avoccado/avoccado-pcb-avr/avoccado-alpha-1/20140912-A1-gerber-files/rendered/ScreenShot_1.png

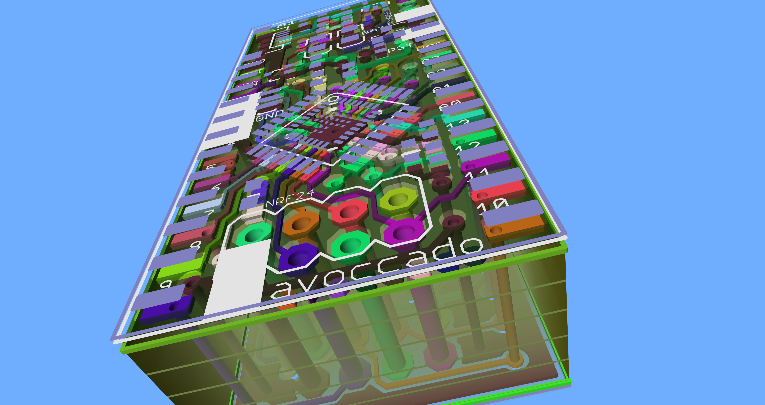
avoccado-alpha-1/20140912-A1-gerber-files/rendered/ScreenShot_1.png
