avoccado/avoccado-pcb-avr/avoccado-faye/avoccado-faye.png

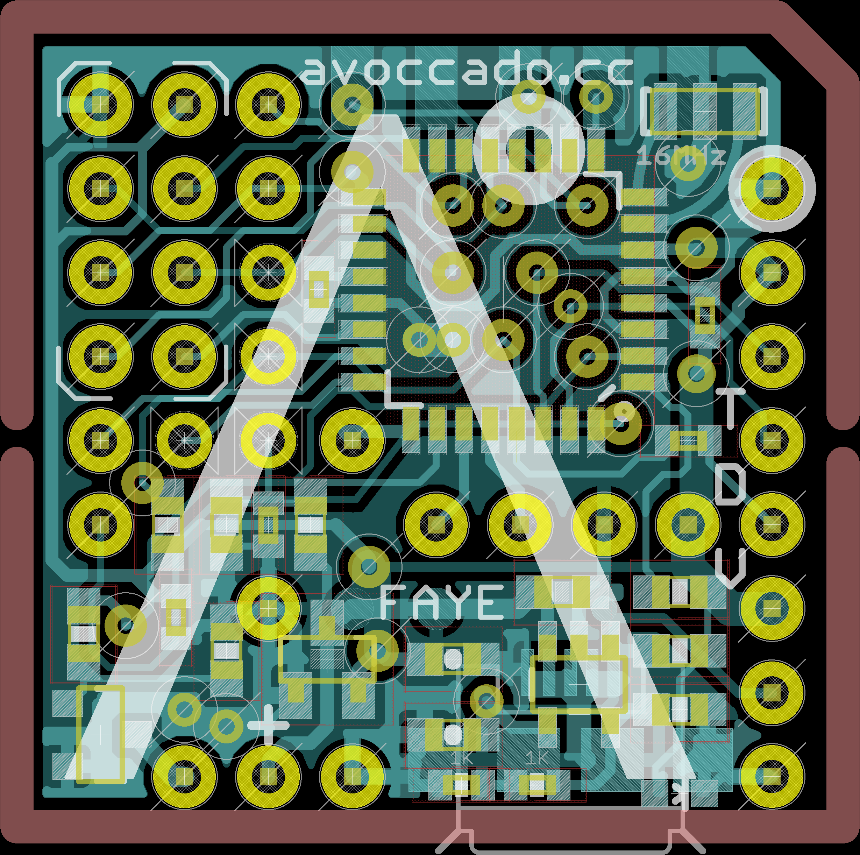
avoccado-faye/avoccado-faye.png
