avoccado/avoccado-pcb-avr/avoccado-felina/avoccado-avr-pcb-felina-all.png

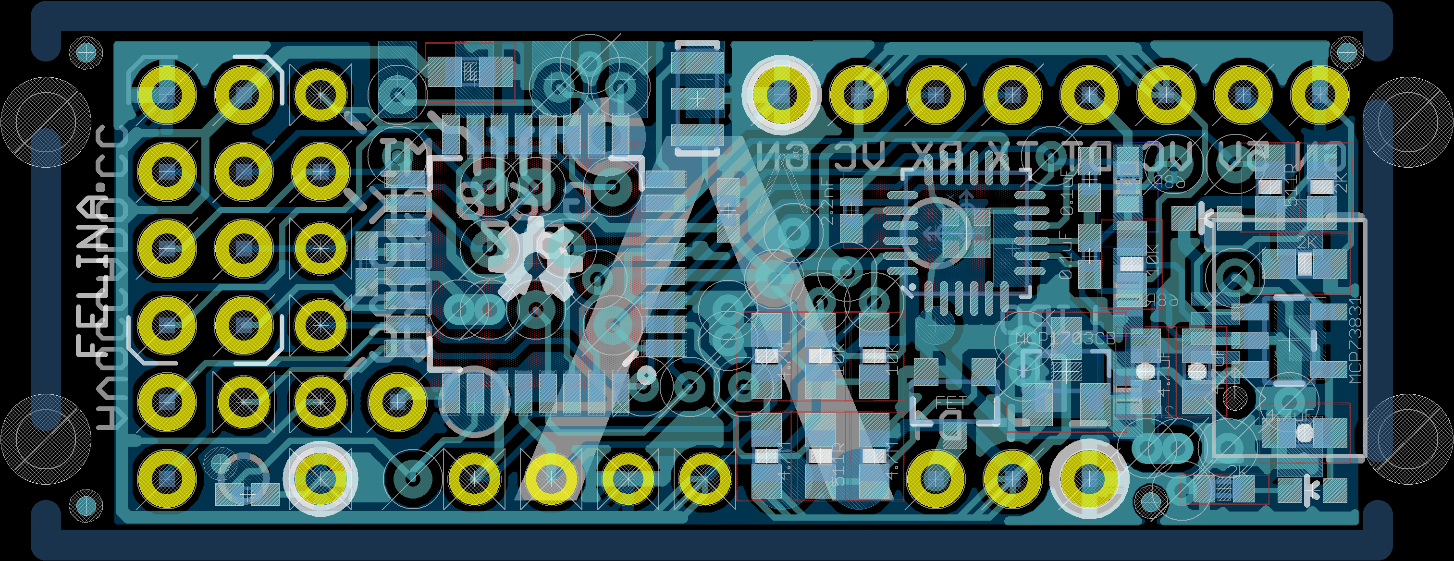
avoccado-felina/avoccado-avr-pcb-felina-all.png
