avoccado/avoccado-pcb-avr/avoccado-felina/avoccado-avr-pcb-felina-bottom.png

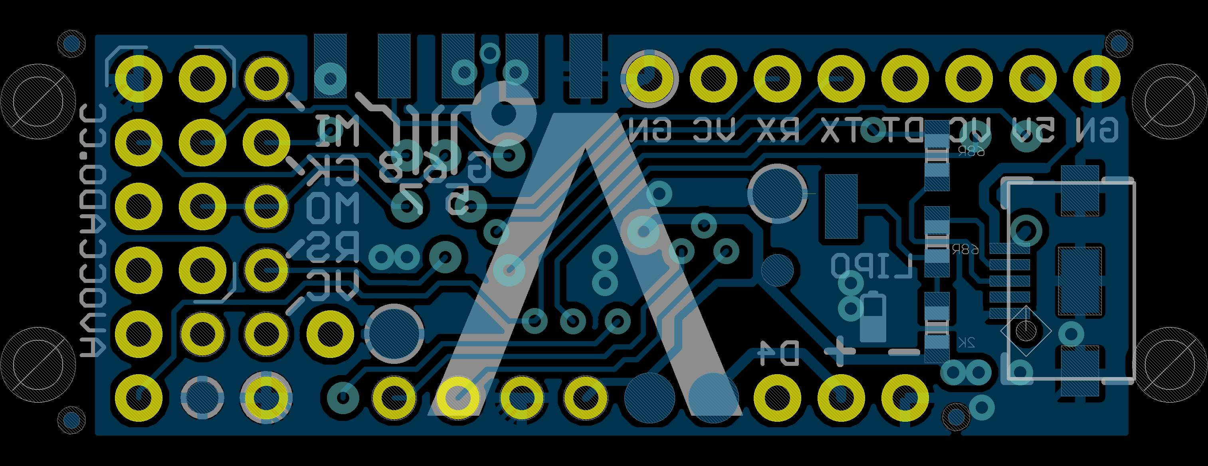
avoccado-felina/avoccado-avr-pcb-felina-bottom.png
