avoccado/avoccado-pcb-avr/avoccado-felina/avoccado-avr-pcb-felina-top.png

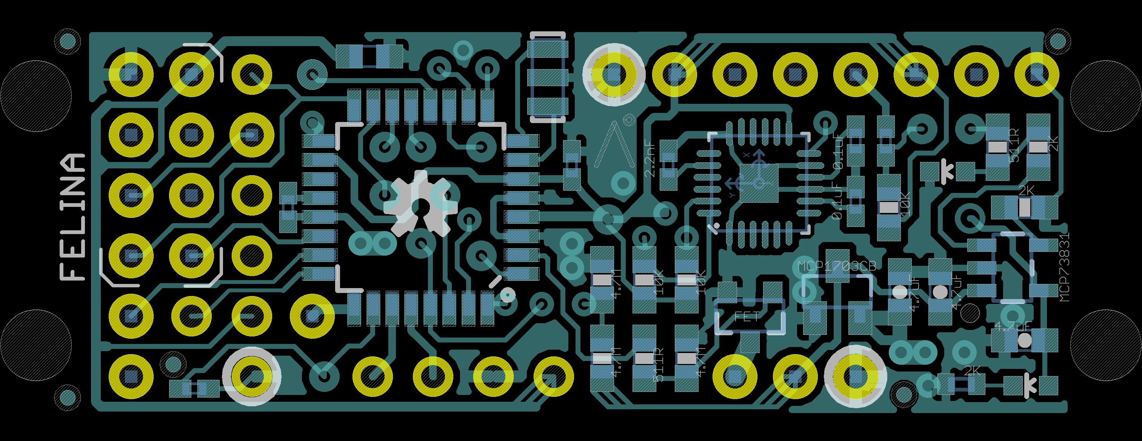
avoccado-felina/avoccado-avr-pcb-felina-top.png
