avoccado/avoccado-pcb-avr/avoccado-gin/avoccado-avr-gin-bot.png

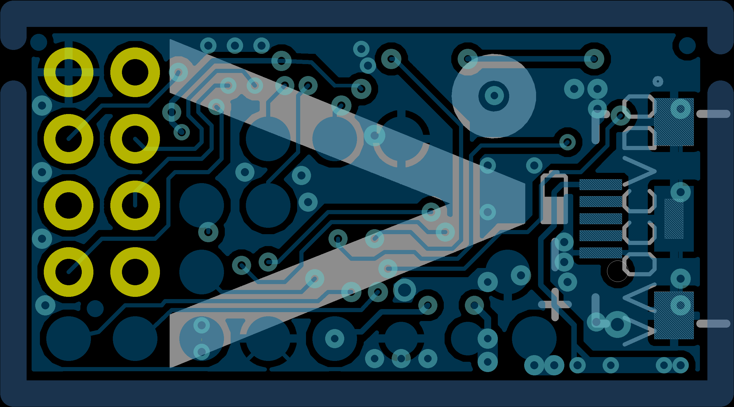
avoccado-gin/avoccado-avr-gin-bot.png
