avoccado/avoccado-pcb-avr/avoccado-nora/nora1-panel/nora1-panel-solder-paste-stencil.png

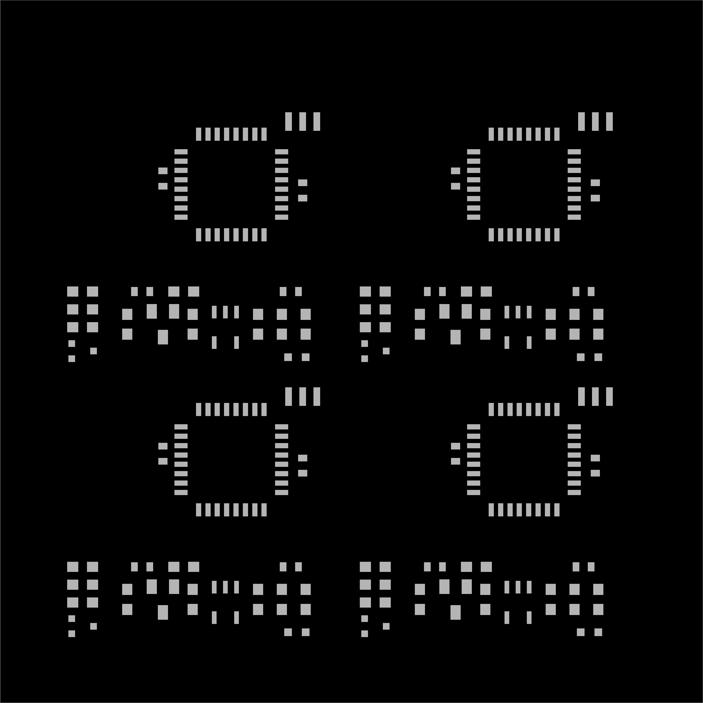
avoccado-nora/nora1-panel/nora1-panel-solder-paste-stencil.png
