avoccado/avoccado-pcb-avr/avoccado-alpha-1/avoccado-avr-pcb.brd

## EAGLE design avoccado-alpha-1/avoccado-avr-pcb.brd (2014-12-11)

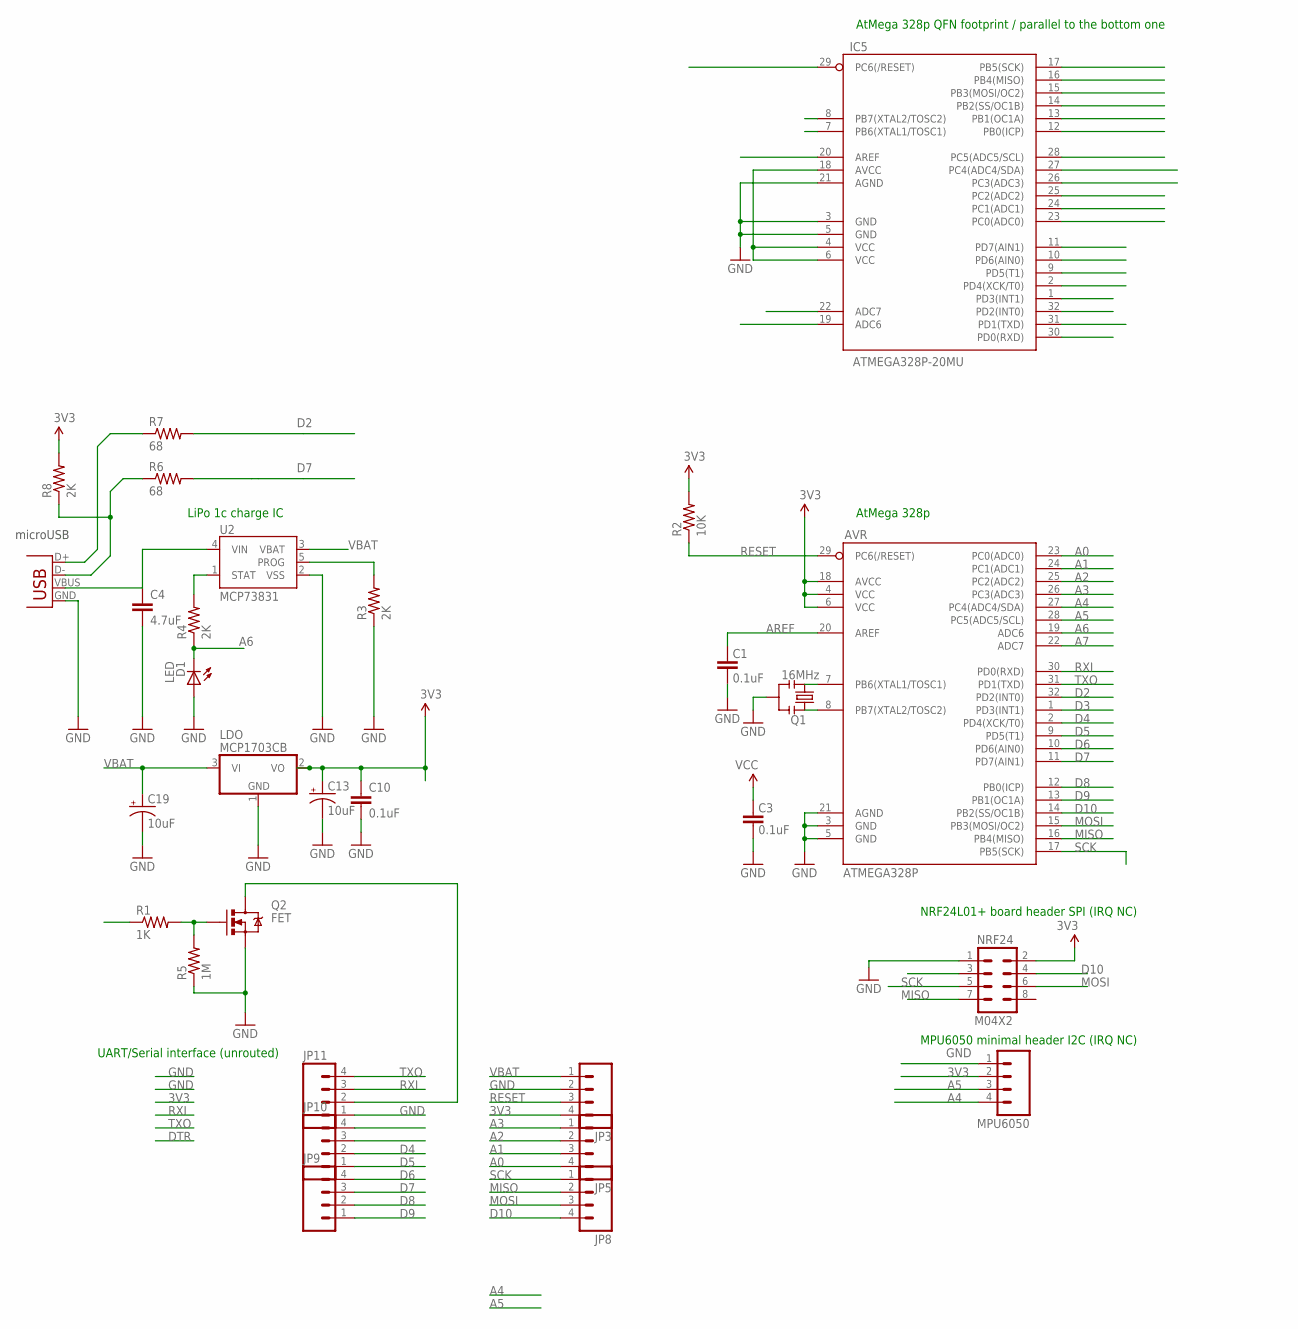
[picture p42: schematic avoccado-avr-pcb.sch]

Parts:
AVR: ATMEGA328P; TQFP32-08
C1, C3, C10: 0.1uF; C0402
C4: 4.7uF; 0603-CAP
C13, C19: 10uF; EIA3216
D1: LED; LED-0603
IC5: ATMEGA328P-20MU; MLF32
JP3, JP5, JP8, JP9, JP10, JP11: M04SMD1X4; 1X04-SMD
LDO: MCP1703CB; SOT23
MPU6050: M041X04_NO_SILK; 1X04_NO_SILK
NRF24: M04X2; 2X4
Q1: 16MHz; RESONATOR-SMD
Q2: FET; SOT323
R1: 1K; 0603-RES
R2: 10K; 0603-RES
R3, R4, R8: 2K; 0603-RES
R5: 1M; 0603-RES
R6, R7: 68; 0603-RES
U2: MCP73831; SOT23-5
X1: Micro USB; USB-MICROB

Connections:
3V3: AVR.4 (VCC), AVR.6 (VCC), AVR.18 (AVCC), C3.2, C10.1, C13.A (+), IC5.4 (VCC), IC5.6 (VCC), IC5.18 (AVCC), JP3.4, LDO.2 (VO), MPU6050.2, NRF24.2, R2.2, R8.2
A0: AVR.23 (PC0(ADC0)), IC5.23 (PC0(ADC0)), JP5.4
A1: AVR.24 (PC1(ADC1)), IC5.24 (PC1(ADC1)), JP5.3
A2: AVR.25 (PC2(ADC2)), IC5.25 (PC2(ADC2)), JP5.2
A3: AVR.26 (PC3(ADC3)), IC5.26 (PC3(ADC3)), JP5.1
A4: AVR.27 (PC4(ADC4/SDA)), IC5.27 (PC4(ADC4/SDA)), MPU6050.4
A5: AVR.28 (PC5(ADC5/SCL)), IC5.28 (PC5(ADC5/SCL)), MPU6050.3
A6: AVR.19 (ADC6), D1.C, IC5.19 (ADC6), R4.1
A7: AVR.22 (ADC7), IC5.22 (ADC7)
AREF: AVR.20 (AREF), C1.2, IC5.20 (AREF)
BUS: C4.1, U2.4 (VIN), X1.VBUS
D2: AVR.32 (PD2(INT0)), IC5.32 (PD2(INT0)), R7.2
D3: AVR.1 (PD3(INT1)), IC5.1 (PD3(INT1)), R1.1
D4: AVR.2 (PD4(XCK/T0)), IC5.2 (PD4(XCK/T0)), JP10.2
D5: AVR.9 (PD5(T1)), IC5.9 (PD5(T1)), JP10.1
D6: AVR.10 (PD6(AIN0)), IC5.10 (PD6(AIN0)), JP9.4
D7: AVR.11 (PD7(AIN1)), IC5.11 (PD7(AIN1)), JP9.3, R6.2
D8: AVR.12 (PB0(ICP)), IC5.12 (PB0(ICP)), JP9.2
D9: AVR.13 (PB1(OC1A)), IC5.13 (PB1(OC1A)), JP9.1, NRF24.3
D10: AVR.14 (PB2(SS/OC1B)), IC5.14 (PB2(SS/OC1B)), JP8.4, NRF24.4
GND: AVR.3 (GND), AVR.5 (GND), AVR.21 (AGND), C1.1, C3.1, C4.2, C10.2, C13.C (-), C19.C (-), D1.A, IC5.3 (GND), IC5.5 (GND), IC5.21 (AGND), JP3.2, JP10.3, JP10.4, JP11.1, LDO.1 (GND), MPU6050.1, NRF24.1, Q1.2, Q2.2 (S), R3.1, R5.1, U2.2 (VSS), X1.GND
MISO: AVR.16 (PB4(MISO)), IC5.16 (PB4(MISO)), JP8.2, NRF24.7
MOSI: AVR.15 (PB3(MOSI/OC2)), IC5.15 (PB3(MOSI/OC2)), JP8.3, NRF24.6
unnamed: AVR.8 (PB7(XTAL2/TOSC2)), IC5.8 (PB7(XTAL2/TOSC2)), Q1.1
unnamed: AVR.7 (PB6(XTAL1/TOSC1)), IC5.7 (PB6(XTAL1/TOSC1)), Q1.3
unnamed: R3.2, U2.5 (PROG)
unnamed: R4.2, U2.1 (STAT)
unnamed: Q2.1 (G), R1.2, R5.2
RESET: AVR.29 (PC6(/RESET)), IC5.29 (PC6(/RESET)), JP3.3, R2.1
RXI: AVR.30 (PD0(RXD)), IC5.30 (PD0(RXD)), JP11.3
SCK: AVR.17 (PB5(SCK)), IC5.17 (PB5(SCK)), JP8.1, NRF24.5
TXO: AVR.31 (PD1(TXD)), IC5.31 (PD1(TXD)), JP11.4
USB-D+: R7.1, X1.D+
USB-D-: R6.1, R8.1, X1.D-
VBAT: C19.A (+), JP3.1, LDO.3 (VI), U2.3 (VBAT)
VIBR: JP11.2, Q2.3 (D)

Notes on the sheet:
microUSB
NRF24L01+ board header SPI (IRQ NC)
MPU6050 minimal header I2C (IRQ NC)
AtMega 328p
AtMega 328p QFN footprint / parallel to the bottom one
LiPo 1c charge IC
UART/Serial interface (unrouted)

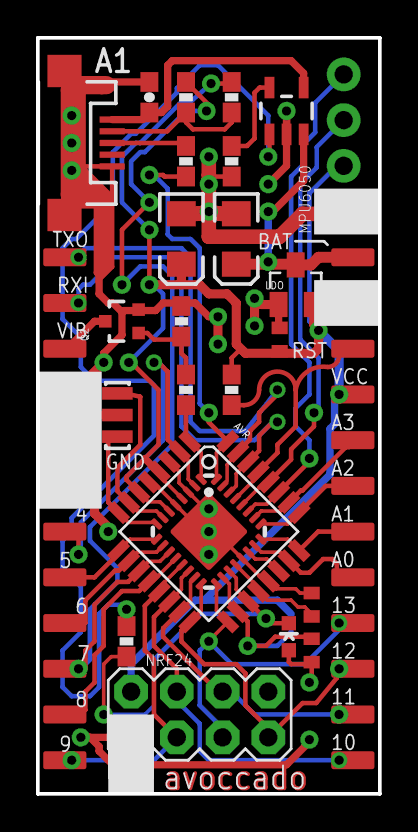
[picture p43: board avoccado-avr-pcb.brd from above]

Board: 2 copper layers, 19.0 x 42.0 mm, 30 parts (0 on the bottom side), 36 nets.
