avoccado/avoccado-pcb-avr/avoccado-yolandi/panel/avoccado-avr-pcb-yolandi-panel.brd

## EAGLE design avoccado-yolandi/panel/avoccado-avr-pcb-yolandi-panel.brd (2015-01-10)

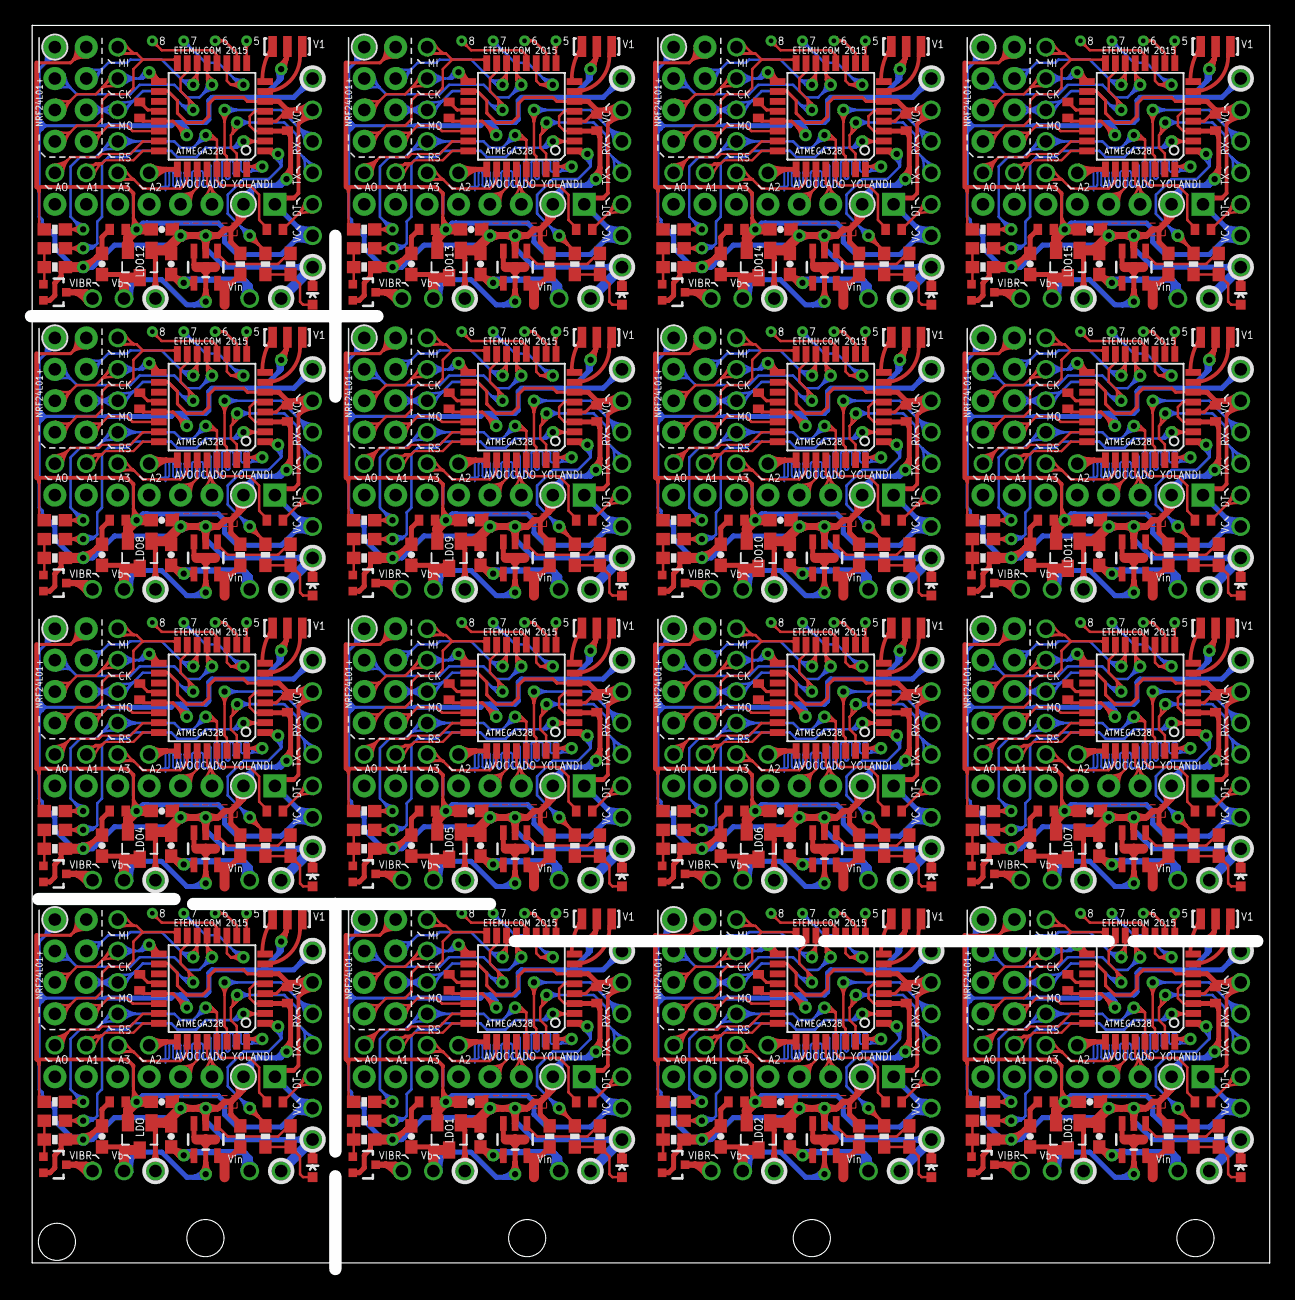
[picture p44: board avoccado-avr-pcb-yolandi-panel.brd from above]

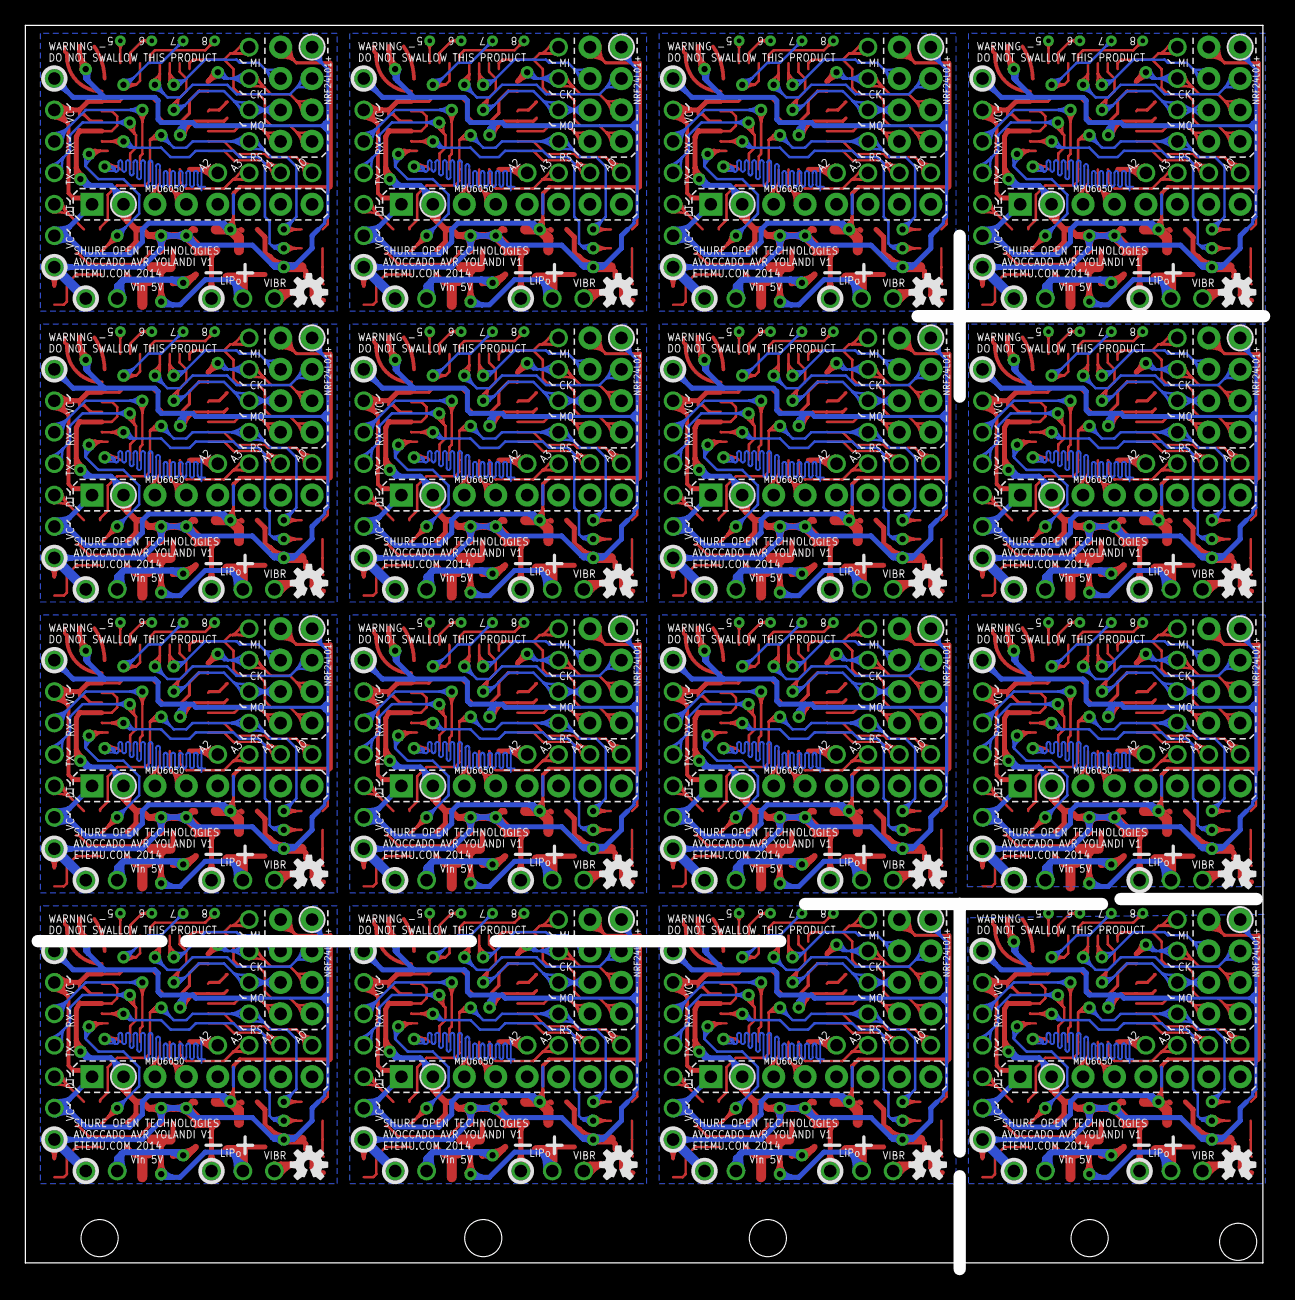
[picture p45: board avoccado-avr-pcb-yolandi-panel.brd from below]

Board: 2 copper layers, 100.0 x 100.0 mm, 784 parts (16 on the bottom side), 544 nets.

Parts:
AVR, AVR1, AVR2, AVR3, AVR4, AVR5, AVR6, AVR7, AVR8, AVR9, AVR10, AVR11, AVR12, AVR13, AVR14, AVR15: ATMEGA328P; TQFP32-08
C1, C2, C3, C7, C8, C9, C10, C12, C15, C16, C17, C19, C22, C23, C24, C26, C29, C30, C31, C33, C36, C37, C38, C40, C43, C44, C45, C47, C50, C51, C52, C54, C57, C58, C59, C61, C64, C65, C66, C68, C71, C72, C73, C75, C78, C79, C80, C82, C85, C86, C87, C89, C92, C93, C94, C96, C99, C100, C101, C103, C106, C107, C108, C110: 0.1uF; C0402
C4, C5, C6, C11, C13, C14, C18, C20, C21, C25, C27, C28, C32, C34, C35, C39, C41, C42, C46, C48, C49, C53, C55, C56, C60, C62, C63, C67, C69, C70, C74, C76, C77, C81, C83, C84, C88, C90, C91, C95, C97, C98, C102, C104, C105, C109, C111, C112: 4.7uF; 0603-CAP
D1, D2, D3, D4, D5, D6, D7, D8, D9, D10, D11, D12, D13, D14, D15, D16: LED; LED-0603
JP1, JP4, JP51, JP76, JP101, JP126, JP151, JP176, JP201, JP226, JP251, JP276, JP301, JP326, JP351, JP376: MPU6050; 1X08_PIN1_NO_SILK
JP2, JP27, JP28, JP29, JP47, JP48, JP49, JP50, JP72, JP73, JP74, JP75, JP97, JP98, JP99, JP100, JP122, JP123, JP124, JP125, JP147, JP148, JP149, JP150, JP172, JP173, JP174, JP175, JP197, JP198, JP199, JP200, JP222, JP223, JP224, JP225, JP247, JP248, JP249, JP250, JP272, JP273, JP274, JP275, JP297, JP298, JP299, JP300, JP322, JP323, JP324, JP325, JP347, JP348, JP349, JP350, JP372, JP373, JP374, JP375, JP397, JP398, JP399, JP400: M021X02_NO_SILK; 1X02_NO_SILK
JP3, JP5, JP6, JP7, JP8, JP9, JP10, JP11, JP12, JP13, JP14, JP15, JP16, JP17, JP18, JP19, JP20, JP21, JP22, JP23, JP24, JP25, JP26, JP30, JP31, JP32, JP33, JP34, JP35, JP36, JP37, JP38, JP39, JP40, JP41, JP42, JP43, JP44, JP45, JP46, JP52, JP53, JP54, JP55, JP56, JP57, JP58, JP59, JP60, JP61, JP62, JP63, JP64, JP65, JP66, JP67, JP68, JP69, JP70, JP71, JP77, JP78, JP79, JP80, JP81, JP82, JP83, JP84, JP85, JP86, JP87, JP88, JP89, JP90, JP91, JP92, JP93, JP94, JP95, JP96, JP102, JP103, JP104, JP105, JP106, JP107, JP108, JP109, JP110, JP111, JP112, JP113, JP114, JP115, JP116, JP117, JP118, JP119, JP120, JP121, JP127, JP128, JP129, JP130, JP131, JP132, JP133, JP134, JP135, JP136, JP137, JP138, JP139, JP140, JP141, JP142, JP143, JP144, JP145, JP146, JP152, JP153, JP154, JP155, JP156, JP157, JP158, JP159, JP160, JP161, JP162, JP163, JP164, JP165, JP166, JP167, JP168, JP169, JP170, JP171, JP177, JP178, JP179, JP180, JP181, JP182, JP183, JP184, JP185, JP186, JP187, JP188, JP189, JP190, JP191, JP192, JP193, JP194, JP195, JP196, JP202, JP203, JP204, JP205, JP206, JP207, JP208, JP209, JP210, JP211, JP212, JP213, JP214, JP215, JP216, JP217, JP218, JP219, JP220, JP221, JP227, JP228, JP229, JP230, JP231, JP232, JP233, JP234, JP235, JP236, JP237, JP238, JP239, JP240, JP241, JP242, JP243, JP244, JP245, JP246, JP252, JP253, JP254, JP255, JP256, JP257, JP258, JP259, JP260, JP261, JP262, JP263, JP264, JP265, JP266, JP267, JP268, JP269, JP270, JP271, JP277, JP278, JP279, JP280, JP281, JP282, JP283, JP284, JP285, JP286, JP287, JP288, JP289, JP290, JP291, JP292, JP293, JP294, JP295, JP296, JP302, JP303, JP304, JP305, JP306, JP307, JP308, JP309, JP310, JP311, JP312, JP313, JP314, JP315, JP316, JP317, JP318, JP319, JP320, JP321, JP327, JP328, JP329, JP330, JP331, JP332, JP333, JP334, JP335, JP336, JP337, JP338, JP339, JP340, JP341, JP342, JP343, JP344, JP345, JP346, JP352, JP353, JP354, JP355, JP356, JP357, JP358, JP359, JP360, JP361, JP362, JP363, JP364, JP365, JP366, JP367, JP368, JP369, JP370, JP371, JP377, JP378, JP379, JP380, JP381, JP382, JP383, JP384, JP385, JP386, JP387, JP388, JP389, JP390, JP391, JP392, JP393, JP394, JP395, JP396: M01NOSILK-KIT; 1X01NS-KIT
LDO, LDO1, LDO2, LDO3, LDO4, LDO5, LDO6, LDO7, LDO8, LDO9, LDO10, LDO11, LDO12, LDO13, LDO14, LDO15: MCP1703CB; SOT23
LOGO1, LOGO2, LOGO3, LOGO4, LOGO5, LOGO6, LOGO7, LOGO8, LOGO9, LOGO10, LOGO11, LOGO12, LOGO13, LOGO14, LOGO15, LOGO16: OSHW-LOGOS; OSHW-LOGO-S
Q1, Q3, Q5, Q7, Q9, Q11, Q13, Q15, Q17, Q19, Q21, Q23, Q25, Q27, Q29, Q31: 16MHz; RESONATOR-SMD
Q2, Q4, Q6, Q8, Q10, Q12, Q14, Q16, Q18, Q20, Q22, Q24, Q26, Q28, Q30, Q32: FET; SOT323
R1, R4, R6, R8, R10, R12, R14, R16, R18, R20, R22, R24, R26, R28, R30, R32, R34, R36, R38, R40, R42, R44, R46, R48, R50, R52, R54, R56, R58, R60, R62, R64, R66, R68, R70, R72, R74, R76, R78, R80, R82, R84, R86, R88, R90, R92, R94, R96: 1K; 0603-RES
R2, R7, R13, R19, R25, R31, R37, R43, R49, R55, R61, R67, R73, R79, R85, R91: 10K; 0603-RES
R3, R9, R15, R21, R27, R33, R39, R45, R51, R57, R63, R69, R75, R81, R87, R93: Rchg; 0603-RES
R5, R11, R17, R23, R29, R35, R41, R47, R53, R59, R65, R71, R77, R83, R89, R95: 1M; 0603-RES
TP1, TP2, TP3, TP4, TP5, TP6, TP7, TP8, TP9, TP10, TP11, TP12, TP13, TP14, TP15, TP16, TP17, TP18, TP19, TP20, TP21, TP22, TP23, TP24, TP25, TP26, TP27, TP28, TP29, TP30, TP31, TP32, TP33, TP34, TP35, TP36, TP37, TP38, TP39, TP40, TP41, TP42, TP43, TP44, TP45, TP46, TP47, TP48, TP49, TP50, TP51, TP52, TP53, TP54, TP55, TP56, TP57, TP58, TP59, TP60, TP61, TP62, TP63, TP64: TEST-POINTTP_15TH_THRU; TP_15TH
U1, U2, U3, U4, U5, U6, U7, U8, U9, U10, U11, U12, U13, U14, U15, U16: MCP73831; SOT23-5

Connections:
3.3V: AVR.4, AVR.6, AVR.18, C3.2, C6.1, C10.1, JP1.1, JP2.2, JP11.1, JP18.1, LDO.2, R2.2
3.3V1: AVR1.4, AVR1.6, AVR1.18, C7.1, C8.2, C14.1, JP4.1, JP31.1, JP38.1, JP47.2, LDO1.2, R7.2
3.3V2: AVR2.4, AVR2.6, AVR2.18, C15.1, C16.2, C21.1, JP51.1, JP56.1, JP63.1, JP72.2, LDO2.2, R13.2
3.3V3: AVR3.4, AVR3.6, AVR3.18, C22.1, C23.2, C28.1, JP76.1, JP81.1, JP88.1, JP97.2, LDO3.2, R19.2
3.3V4: AVR4.4, AVR4.6, AVR4.18, C29.1, C30.2, C35.1, JP101.1, JP106.1, JP113.1, JP122.2, LDO4.2, R25.2
3.3V5: AVR5.4, AVR5.6, AVR5.18, C36.1, C37.2, C42.1, JP126.1, JP131.1, JP138.1, JP147.2, LDO5.2, R31.2
3.3V6: AVR6.4, AVR6.6, AVR6.18, C43.1, C44.2, C49.1, JP151.1, JP156.1, JP163.1, JP172.2, LDO6.2, R37.2
3.3V7: AVR7.4, AVR7.6, AVR7.18, C50.1, C51.2, C56.1, JP176.1, JP181.1, JP188.1, JP197.2, LDO7.2, R43.2
3.3V8: AVR8.4, AVR8.6, AVR8.18, C57.1, C58.2, C63.1, JP201.1, JP206.1, JP213.1, JP222.2, LDO8.2, R49.2
3.3V9: AVR9.4, AVR9.6, AVR9.18, C64.1, C65.2, C70.1, JP226.1, JP231.1, JP238.1, JP247.2, LDO9.2, R55.2
3.3V10: AVR10.4, AVR10.6, AVR10.18, C71.1, C72.2, C77.1, JP251.1, JP256.1, JP263.1, JP272.2, LDO10.2, R61.2
3.3V11: AVR11.4, AVR11.6, AVR11.18, C78.1, C79.2, C84.1, JP276.1, JP281.1, JP288.1, JP297.2, LDO11.2, R67.2
3.3V12: AVR12.4, AVR12.6, AVR12.18, C85.1, C86.2, C91.1, JP301.1, JP306.1, JP313.1, JP322.2, LDO12.2, R73.2
3.3V13: AVR13.4, AVR13.6, AVR13.18, C92.1, C93.2, C98.1, JP326.1, JP331.1, JP338.1, JP347.2, LDO13.2, R79.2
3.3V14: AVR14.4, AVR14.6, AVR14.18, C99.1, C100.2, C105.1, JP351.1, JP356.1, JP363.1, JP372.2, LDO14.2, R85.2
3.3V15: AVR15.4, AVR15.6, AVR15.18, C106.1, C107.2, C112.1, JP376.1, JP381.1, JP388.1, JP397.2, LDO15.2, R91.2
5V: C4.1, JP17.1, U2.4
5V1: C11.1, JP37.1, U1.4
5V2: C18.1, JP62.1, U3.4
5V3: C25.1, JP87.1, U4.4
5V4: C32.1, JP112.1, U5.4
5V5: C39.1, JP137.1, U6.4
5V6: C46.1, JP162.1, U7.4
5V7: C53.1, JP187.1, U8.4
5V8: C60.1, JP212.1, U9.4
5V9: C67.1, JP237.1, U10.4
5V10: C74.1, JP262.1, U11.4
5V11: C81.1, JP287.1, U12.4
5V12: C88.1, JP312.1, U13.4
5V13: C95.1, JP337.1, U14.4
5V14: C102.1, JP362.1, U15.4
5V15: C109.1, JP387.1, U16.4
A0: AVR.23, JP19.1
A1: AVR.24, JP20.1
A2: AVR.25, JP21.1
A3: AVR.26, JP22.1
A4: AVR.27, JP1.4
A5: AVR.28, JP1.3
A7: AVR1.28, JP4.3
A7-NRF-IRQ: AVR.22, JP29.2
A7-NRF-IRQ1: AVR1.22, JP50.2
A7-NRF-IRQ2: AVR2.22, JP75.2
A7-NRF-IRQ3: AVR3.22, JP100.2
A7-NRF-IRQ4: AVR4.22, JP125.2
A7-NRF-IRQ5: AVR5.22, JP150.2
A7-NRF-IRQ6: AVR6.22, JP175.2
A7-NRF-IRQ7: AVR7.22, JP200.2
A7-NRF-IRQ8: AVR8.22, JP225.2
A7-NRF-IRQ9: AVR9.22, JP250.2
A7-NRF-IRQ10: AVR10.22, JP275.2
A7-NRF-IRQ11: AVR11.22, JP300.2
A7-NRF-IRQ12: AVR12.22, JP325.2
A7-NRF-IRQ13: AVR13.22, JP350.2
A7-NRF-IRQ14: AVR14.22, JP375.2
A7-NRF-IRQ15: AVR15.22, JP400.2
A8: AVR1.27, JP4.4
A9: AVR1.26, JP42.1
A10: AVR1.25, JP41.1
A11: AVR1.24, JP40.1
A12: AVR1.23, JP39.1
A14: AVR2.28, JP51.3
A15: AVR2.27, JP51.4
A16: AVR2.26, JP67.1
A17: AVR2.25, JP66.1
A18: AVR2.24, JP65.1
A19: AVR2.23, JP64.1
A21: AVR3.28, JP76.3
A22: AVR3.27, JP76.4
A23: AVR3.26, JP92.1
A24: AVR3.25, JP91.1
A25: AVR3.24, JP90.1
A26: AVR3.23, JP89.1
A28: AVR4.28, JP101.3
A29: AVR4.27, JP101.4
A30: AVR4.26, JP117.1
A31: AVR4.25, JP116.1
A32: AVR4.24, JP115.1
A33: AVR4.23, JP114.1
A35: AVR5.28, JP126.3
A36: AVR5.27, JP126.4
A37: AVR5.26, JP142.1
A38: AVR5.25, JP141.1
A39: AVR5.24, JP140.1
A40: AVR5.23, JP139.1
A42: AVR6.28, JP151.3
A43: AVR6.27, JP151.4
A44: AVR6.26, JP167.1
A45: AVR6.25, JP166.1
A46: AVR6.24, JP165.1
A47: AVR6.23, JP164.1
A49: AVR7.28, JP176.3
A50: AVR7.27, JP176.4
A51: AVR7.26, JP192.1
A52: AVR7.25, JP191.1
A53: AVR7.24, JP190.1
A54: AVR7.23, JP189.1
A56: AVR8.28, JP201.3
A57: AVR8.27, JP201.4
A58: AVR8.26, JP217.1
A59: AVR8.25, JP216.1
A60: AVR8.24, JP215.1
A61: AVR8.23, JP214.1
A63: AVR9.28, JP226.3
A64: AVR9.27, JP226.4
A65: AVR9.26, JP242.1
A66: AVR9.25, JP241.1
A67: AVR9.24, JP240.1
A68: AVR9.23, JP239.1
A70: AVR10.28, JP251.3
A71: AVR10.27, JP251.4
A72: AVR10.26, JP267.1
A73: AVR10.25, JP266.1
A74: AVR10.24, JP265.1
A75: AVR10.23, JP264.1
A77: AVR11.28, JP276.3
A78: AVR11.27, JP276.4
A79: AVR11.26, JP292.1
A80: AVR11.25, JP291.1
A81: AVR11.24, JP290.1
A82: AVR11.23, JP289.1
A84: AVR12.28, JP301.3
A85: AVR12.27, JP301.4
A86: AVR12.26, JP317.1
A87: AVR12.25, JP316.1
A88: AVR12.24, JP315.1
A89: AVR12.23, JP314.1
A91: AVR13.28, JP326.3
A92: AVR13.27, JP326.4
A93: AVR13.26, JP342.1
A94: AVR13.25, JP341.1
A95: AVR13.24, JP340.1
A96: AVR13.23, JP339.1
A98: AVR14.28, JP351.3
A99: AVR14.27, JP351.4
A100: AVR14.26, JP367.1
A101: AVR14.25, JP366.1
A102: AVR14.24, JP365.1
A103: AVR14.23, JP364.1
A105: AVR15.28, JP376.3
A106: AVR15.27, JP376.4
A107: AVR15.26, JP392.1
A108: AVR15.25, JP391.1
A109: AVR15.24, JP390.1
A110: AVR15.23, JP389.1
AREF: AVR.20, C1.2
AREF1: AVR1.20, C9.2
AREF2: AVR2.20, C17.2
AREF3: AVR3.20, C24.2
AREF4: AVR4.20, C31.2
AREF5: AVR5.20, C38.2
AREF6: AVR6.20, C45.2
AREF7: AVR7.20, C52.2
AREF8: AVR8.20, C59.2
AREF9: AVR9.20, C66.2
AREF10: AVR10.20, C73.2
AREF11: AVR11.20, C80.2
AREF12: AVR12.20, C87.2
AREF13: AVR13.20, C94.2
AREF14: AVR14.20, C101.2
AREF15: AVR15.20, C108.2
CHG-PROG: R3.2, U2.5
CHG-PROG1: R9.2, U1.5
CHG-PROG2: R15.2, U3.5
CHG-PROG3: R21.2, U4.5
CHG-PROG4: R27.2, U5.5
CHG-PROG5: R33.2, U6.5
CHG-PROG6: R39.2, U7.5
CHG-PROG7: R45.2, U8.5
CHG-PROG8: R51.2, U9.5
CHG-PROG9: R57.2, U10.5
CHG-PROG10: R63.2, U11.5
CHG-PROG11: R69.2, U12.5
CHG-PROG12: R75.2, U13.5
CHG-PROG13: R81.2, U14.5
CHG-PROG14: R87.2, U15.5
CHG-PROG15: R93.2, U16.5
D1: AVR1.13, JP48.1
D3: AVR.1, R6.1
D4: AVR.2, R1.1
D5: AVR.9, TP1.P$1
D6: AVR.10, TP6.P$1
D7: AVR.11, TP7.P$1
D8: AVR.12, TP8.P$1
D9: AVR.13, JP27.1
D10: AVR.14, JP27.2
D11: AVR1.12, TP5.P$1
D13: AVR1.1, R12.1
D14: AVR1.2, R8.1
D15: AVR1.9, TP2.P$1
D16: AVR1.10, TP3.P$1
D17: AVR1.11, TP4.P$1
D18: AVR1.14, JP48.2
D19: AVR2.13, JP73.1
D20: AVR2.12, TP12.P$1
D22: AVR2.1, R18.1
D23: AVR2.2, R14.1
D24: AVR2.9, TP9.P$1
D25: AVR2.10, TP10.P$1
D26: AVR2.11, TP11.P$1
D27: AVR2.14, JP73.2
D28: AVR3.13, JP98.1
D29: AVR3.12, TP16.P$1
D31: AVR3.1, R24.1
D32: AVR3.2, R20.1
D33: AVR3.9, TP13.P$1
D34: AVR3.10, TP14.P$1
D35: AVR3.11, TP15.P$1
D36: AVR3.14, JP98.2
D37: AVR4.13, JP123.1
D38: AVR4.12, TP20.P$1
D40: AVR4.1, R30.1
D41: AVR4.2, R26.1
D42: AVR4.9, TP17.P$1
D43: AVR4.10, TP18.P$1
D44: AVR4.11, TP19.P$1
D45: AVR4.14, JP123.2
D46: AVR5.13, JP148.1
D47: AVR5.12, TP24.P$1
D49: AVR5.1, R36.1
D50: AVR5.2, R32.1
D51: AVR5.9, TP21.P$1
D52: AVR5.10, TP22.P$1
D53: AVR5.11, TP23.P$1
D54: AVR5.14, JP148.2
D55: AVR6.13, JP173.1
D56: AVR6.12, TP28.P$1
D58: AVR6.1, R42.1
D59: AVR6.2, R38.1
D60: AVR6.9, TP25.P$1
D61: AVR6.10, TP26.P$1
D62: AVR6.11, TP27.P$1
D63: AVR6.14, JP173.2
D64: AVR7.13, JP198.1
D65: AVR7.12, TP32.P$1
D67: AVR7.1, R48.1
D68: AVR7.2, R44.1
D69: AVR7.9, TP29.P$1
D70: AVR7.10, TP30.P$1
D71: AVR7.11, TP31.P$1
D72: AVR7.14, JP198.2
D73: AVR8.13, JP223.1
D74: AVR8.12, TP36.P$1
D76: AVR8.1, R54.1
D77: AVR8.2, R50.1
D78: AVR8.9, TP33.P$1
D79: AVR8.10, TP34.P$1
D80: AVR8.11, TP35.P$1
D81: AVR8.14, JP223.2
D82: AVR9.13, JP248.1
D83: AVR9.12, TP40.P$1
D85: AVR9.1, R60.1
D86: AVR9.2, R56.1
D87: AVR9.9, TP37.P$1
D88: AVR9.10, TP38.P$1
D89: AVR9.11, TP39.P$1
D90: AVR9.14, JP248.2
D91: AVR10.13, JP273.1
D92: AVR10.12, TP44.P$1
D94: AVR10.1, R66.1
D95: AVR10.2, R62.1
D96: AVR10.9, TP41.P$1
D97: AVR10.10, TP42.P$1
D98: AVR10.11, TP43.P$1
D99: AVR10.14, JP273.2
D100: AVR11.13, JP298.1
D101: AVR11.12, TP48.P$1
D103: AVR11.1, R72.1
D104: AVR11.2, R68.1
D105: AVR11.9, TP45.P$1
D106: AVR11.10, TP46.P$1
D107: AVR11.11, TP47.P$1
D108: AVR11.14, JP298.2
D109: AVR12.13, JP323.1
D110: AVR12.12, TP52.P$1
D112: AVR12.1, R78.1
D113: AVR12.2, R74.1
D114: AVR12.9, TP49.P$1
D115: AVR12.10, TP50.P$1
D116: AVR12.11, TP51.P$1
D117: AVR12.14, JP323.2
D118: AVR13.13, JP348.1
D119: AVR13.12, TP56.P$1
D121: AVR13.1, R84.1
D122: AVR13.2, R80.1
D123: AVR13.9, TP53.P$1
D124: AVR13.10, TP54.P$1
D125: AVR13.11, TP55.P$1
D126: AVR13.14, JP348.2
D127: AVR14.13, JP373.1
D128: AVR14.12, TP60.P$1
D130: AVR14.1, R90.1
D131: AVR14.2, R86.1
D132: AVR14.9, TP57.P$1
D133: AVR14.10, TP58.P$1
D134: AVR14.11, TP59.P$1
D135: AVR14.14, JP373.2
D136: AVR15.13, JP398.1
D137: AVR15.12, TP64.P$1
D139: AVR15.1, R96.1
D140: AVR15.2, R92.1
D141: AVR15.9, TP61.P$1
D142: AVR15.10, TP62.P$1
D143: AVR15.11, TP63.P$1
D144: AVR15.14, JP398.2
DTR: C2.2, JP10.1
DTR1: C12.2, JP30.1
DTR2: C19.2, JP55.1
DTR3: C26.2, JP80.1
DTR4: C33.2, JP105.1
DTR5: C40.2, JP130.1
DTR6: C47.2, JP155.1
DTR7: C54.2, JP180.1
DTR8: C61.2, JP205.1
DTR9: C68.2, JP230.1
DTR10: C75.2, JP255.1
DTR11: C82.2, JP280.1
DTR12: C89.2, JP305.1
DTR13: C96.2, JP330.1
DTR14: C103.2, JP355.1
DTR15: C110.2, JP380.1
GND: AVR.3, AVR.5, AVR.21, C1.1, C3.1, C4.2, C5.2, C6.2, C10.2, D1.C, JP1.2, JP2.1, JP3.1, JP6.1, JP25.1, JP26.1, LDO.1, Q1.2, Q2.2, R3.1, R5.1, U2.2
GND1: AVR1.3, AVR1.5, AVR1.21, C7.2, C8.1, C9.1, C11.2, C13.2, C14.2, D2.C, JP4.2, JP5.1, JP36.1, JP45.1, JP46.1, JP47.1, LDO1.1, Q3.2, Q4.2, R9.1, R11.1, U1.2
GND2: AVR2.3, AVR2.5, AVR2.21, C15.2, C16.1, C17.1, C18.2, C20.2, C21.2, D3.C, JP51.2, JP52.1, JP61.1, JP70.1, JP71.1, JP72.1, LDO2.1, Q5.2, Q6.2, R15.1, R17.1, U3.2
GND3: AVR3.3, AVR3.5, AVR3.21, C22.2, C23.1, C24.1, C25.2, C27.2, C28.2, D4.C, JP76.2, JP77.1, JP86.1, JP95.1, JP96.1, JP97.1, LDO3.1, Q7.2, Q8.2, R21.1, R23.1, U4.2
GND4: AVR4.3, AVR4.5, AVR4.21, C29.2, C30.1, C31.1, C32.2, C34.2, C35.2, D5.C, JP101.2, JP102.1, JP111.1, JP120.1, JP121.1, JP122.1, LDO4.1, Q9.2, Q10.2, R27.1, R29.1, U5.2
GND5: AVR5.3, AVR5.5, AVR5.21, C36.2, C37.1, C38.1, C39.2, C41.2, C42.2, D6.C, JP126.2, JP127.1, JP136.1, JP145.1, JP146.1, JP147.1, LDO5.1, Q11.2, Q12.2, R33.1, R35.1, U6.2
GND6: AVR6.3, AVR6.5, AVR6.21, C43.2, C44.1, C45.1, C46.2, C48.2, C49.2, D7.C, JP151.2, JP152.1, JP161.1, JP170.1, JP171.1, JP172.1, LDO6.1, Q13.2, Q14.2, R39.1, R41.1, U7.2
GND7: AVR7.3, AVR7.5, AVR7.21, C50.2, C51.1, C52.1, C53.2, C55.2, C56.2, D8.C, JP176.2, JP177.1, JP186.1, JP195.1, JP196.1, JP197.1, LDO7.1, Q15.2, Q16.2, R45.1, R47.1, U8.2
GND8: AVR8.3, AVR8.5, AVR8.21, C57.2, C58.1, C59.1, C60.2, C62.2, C63.2, D9.C, JP201.2, JP202.1, JP211.1, JP220.1, JP221.1, JP222.1, LDO8.1, Q17.2, Q18.2, R51.1, R53.1, U9.2
GND9: AVR9.3, AVR9.5, AVR9.21, C64.2, C65.1, C66.1, C67.2, C69.2, C70.2, D10.C, JP226.2, JP227.1, JP236.1, JP245.1, JP246.1, JP247.1, LDO9.1, Q19.2, Q20.2, R57.1, R59.1, U10.2
GND10: AVR10.3, AVR10.5, AVR10.21, C71.2, C72.1, C73.1, C74.2, C76.2, C77.2, D11.C, JP251.2, JP252.1, JP261.1, JP270.1, JP271.1, JP272.1, LDO10.1, Q21.2, Q22.2, R63.1, R65.1, U11.2
GND11: AVR11.3, AVR11.5, AVR11.21, C78.2, C79.1, C80.1, C81.2, C83.2, C84.2, D12.C, JP276.2, JP277.1, JP286.1, JP295.1, JP296.1, JP297.1, LDO11.1, Q23.2, Q24.2, R69.1, R71.1, U12.2
GND12: AVR12.3, AVR12.5, AVR12.21, C85.2, C86.1, C87.1, C88.2, C90.2, C91.2, D13.C, JP301.2, JP302.1, JP311.1, JP320.1, JP321.1, JP322.1, LDO12.1, Q25.2, Q26.2, R75.1, R77.1, U13.2
GND13: AVR13.3, AVR13.5, AVR13.21, C92.2, C93.1, C94.1, C95.2, C97.2, C98.2, D14.C, JP326.2, JP327.1, JP336.1, JP345.1, JP346.1, JP347.1, LDO13.1, Q27.2, Q28.2, R81.1, R83.1, U14.2
GND14: AVR14.3, AVR14.5, AVR14.21, C99.2, C100.1, C101.1, C102.2, C104.2, C105.2, D15.C, JP351.2, JP352.1, JP361.1, JP370.1, JP371.1, JP372.1, LDO14.1, Q29.2, Q30.2, R87.1, R89.1, U15.2
GND15: AVR15.3, AVR15.5, AVR15.21, C106.2, C107.1, C108.1, C109.2, C111.2, C112.2, D16.C, JP376.2, JP377.1, JP386.1, JP395.1, JP396.1, JP397.1, LDO15.1, Q31.2, Q32.2, R93.1, R95.1, U16.2
LED: D1.A, R4.1, R6.2
LED1: D2.A, R10.1, R12.2
LED2: D3.A, R16.1, R18.2
LED3: D4.A, R22.1, R24.2
LED4: D5.A, R28.1, R30.2
LED5: D6.A, R34.1, R36.2
LED6: D7.A, R40.1, R42.2
LED7: D8.A, R46.1, R48.2
LED8: D9.A, R52.1, R54.2
LED9: D10.A, R58.1, R60.2
LED10: D11.A, R64.1, R66.2
LED11: D12.A, R70.1, R72.2
LED12: D13.A, R76.1, R78.2
LED13: D14.A, R82.1, R84.2
LED14: D15.A, R88.1, R90.2
LED15: D16.A, R94.1, R96.2
MISO: AVR.16, JP12.1, JP29.1
MISO1: AVR1.16, JP32.1, JP50.1
MISO2: AVR2.16, JP57.1, JP75.1
MISO3: AVR3.16, JP82.1, JP100.1
MISO4: AVR4.16, JP107.1, JP125.1
MISO5: AVR5.16, JP132.1, JP150.1
MISO6: AVR6.16, JP157.1, JP175.1
MISO7: AVR7.16, JP182.1, JP200.1
MISO8: AVR8.16, JP207.1, JP225.1
MISO9: AVR9.16, JP232.1, JP250.1
MISO10: AVR10.16, JP257.1, JP275.1
MISO11: AVR11.16, JP282.1, JP300.1
MISO12: AVR12.16, JP307.1, JP325.1
MISO13: AVR13.16, JP332.1, JP350.1
MISO14: AVR14.16, JP357.1, JP375.1
MISO15: AVR15.16, JP382.1, JP400.1
MOSI: AVR.15, JP14.1, JP28.2
MOSI1: AVR1.15, JP34.1, JP49.2
MOSI2: AVR2.15, JP59.1, JP74.2
MOSI3: AVR3.15, JP84.1, JP99.2
MOSI4: AVR4.15, JP109.1, JP124.2
MOSI5: AVR5.15, JP134.1, JP149.2
MOSI6: AVR6.15, JP159.1, JP174.2
MOSI7: AVR7.15, JP184.1, JP199.2
MOSI8: AVR8.15, JP209.1, JP224.2
MOSI9: AVR9.15, JP234.1, JP249.2
MOSI10: AVR10.15, JP259.1, JP274.2
MOSI11: AVR11.15, JP284.1, JP299.2
MOSI12: AVR12.15, JP309.1, JP324.2
MOSI13: AVR13.15, JP334.1, JP349.2
MOSI14: AVR14.15, JP359.1, JP374.2
MOSI15: AVR15.15, JP384.1, JP399.2
unnamed: AVR.8, Q1.1
unnamed: AVR.7, Q1.3
unnamed: AVR1.8, Q3.1
unnamed: AVR1.7, Q3.3
unnamed: Q4.1, R8.2, R11.2
unnamed: Q2.1, R1.2, R5.2
unnamed: AVR2.8, Q5.1
unnamed: AVR2.7, Q5.3
unnamed: Q6.1, R14.2, R17.2
unnamed: AVR3.8, Q7.1
unnamed: AVR3.7, Q7.3
unnamed: Q8.1, R20.2, R23.2
unnamed: AVR4.8, Q9.1
unnamed: AVR4.7, Q9.3
unnamed: Q10.1, R26.2, R29.2
unnamed: AVR5.8, Q11.1
unnamed: AVR5.7, Q11.3
unnamed: Q12.1, R32.2, R35.2
unnamed: AVR6.8, Q13.1
unnamed: AVR6.7, Q13.3
unnamed: Q14.1, R38.2, R41.2
unnamed: AVR7.8, Q15.1
unnamed: AVR7.7, Q15.3
unnamed: Q16.1, R44.2, R47.2
unnamed: AVR8.8, Q17.1
unnamed: AVR8.7, Q17.3
unnamed: Q18.1, R50.2, R53.2
unnamed: AVR9.8, Q19.1
unnamed: AVR9.7, Q19.3
unnamed: Q20.1, R56.2, R59.2
unnamed: AVR10.8, Q21.1
unnamed: AVR10.7, Q21.3
unnamed: Q22.1, R62.2, R65.2
unnamed: AVR11.8, Q23.1
unnamed: AVR11.7, Q23.3
unnamed: Q24.1, R68.2, R71.2
unnamed: AVR12.8, Q25.1
unnamed: AVR12.7, Q25.3
unnamed: Q26.1, R74.2, R77.2
unnamed: AVR13.8, Q27.1
unnamed: AVR13.7, Q27.3
unnamed: Q28.1, R80.2, R83.2
unnamed: AVR14.8, Q29.1
unnamed: AVR14.7, Q29.3
unnamed: Q30.1, R86.2, R89.2
unnamed: AVR15.8, Q31.1
unnamed: AVR15.7, Q31.3
unnamed: Q32.1, R92.2, R95.2
RESET: AVR.29, C2.1, JP15.1, R2.1
RESET1: AVR1.29, C12.1, JP35.1, R7.1
RESET2: AVR2.29, C19.1, JP60.1, R13.1
RESET3: AVR3.29, C26.1, JP85.1, R19.1
RESET4: AVR4.29, C33.1, JP110.1, R25.1
RESET5: AVR5.29, C40.1, JP135.1, R31.1
RESET6: AVR6.29, C47.1, JP160.1, R37.1
RESET7: AVR7.29, C54.1, JP185.1, R43.1
RESET8: AVR8.29, C61.1, JP210.1, R49.1
RESET9: AVR9.29, C68.1, JP235.1, R55.1
RESET10: AVR10.29, C75.1, JP260.1, R61.1
RESET11: AVR11.29, C82.1, JP285.1, R67.1
RESET12: AVR12.29, C89.1, JP310.1, R73.1
RESET13: AVR13.29, C96.1, JP335.1, R79.1
RESET14: AVR14.29, C103.1, JP360.1, R85.1
RESET15: AVR15.29, C110.1, JP385.1, R91.1
RXI: AVR.30, JP8.1
RXI1: AVR1.30, JP7.1
RXI2: AVR2.30, JP53.1
RXI3: AVR3.30, JP78.1
RXI4: AVR4.30, JP103.1
RXI5: AVR5.30, JP128.1
RXI6: AVR6.30, JP153.1
RXI7: AVR7.30, JP178.1
RXI8: AVR8.30, JP203.1
RXI9: AVR9.30, JP228.1
RXI10: AVR10.30, JP253.1
RXI11: AVR11.30, JP278.1
RXI12: AVR12.30, JP303.1
RXI13: AVR13.30, JP328.1
RXI14: AVR14.30, JP353.1
RXI15: AVR15.30, JP378.1
SCK: AVR.17, JP13.1, JP28.1
SCK1: AVR1.17, JP33.1, JP49.1
SCK2: AVR2.17, JP58.1, JP74.1
SCK3: AVR3.17, JP83.1, JP99.1
SCK4: AVR4.17, JP108.1, JP124.1
SCK5: AVR5.17, JP133.1, JP149.1
SCK6: AVR6.17, JP158.1, JP174.1
SCK7: AVR7.17, JP183.1, JP199.1
SCK8: AVR8.17, JP208.1, JP224.1
SCK9: AVR9.17, JP233.1, JP249.1
SCK10: AVR10.17, JP258.1, JP274.1
SCK11: AVR11.17, JP283.1, JP299.1
SCK12: AVR12.17, JP308.1, JP324.1
SCK13: AVR13.17, JP333.1, JP349.1
SCK14: AVR14.17, JP358.1, JP374.1
SCK15: AVR15.17, JP383.1, JP399.1
SOC: R4.2, U2.1
SOC1: R10.2, U1.1
SOC2: R16.2, U3.1
SOC3: R22.2, U4.1
SOC4: R28.2, U5.1
SOC5: R34.2, U6.1
SOC6: R40.2, U7.1
SOC7: R46.2, U8.1
SOC8: R52.2, U9.1
SOC9: R58.2, U10.1
SOC10: R64.2, U11.1
SOC11: R70.2, U12.1
SOC12: R76.2, U13.1
SOC13: R82.2, U14.1
SOC14: R88.2, U15.1
SOC15: R94.2, U16.1
TXO: AVR.31, JP9.1
TXO1: AVR1.31, JP16.1
TXO2: AVR2.31, JP54.1
TXO3: AVR3.31, JP79.1
TXO4: AVR4.31, JP104.1
TXO5: AVR5.31, JP129.1
TXO6: AVR6.31, JP154.1
TXO7: AVR7.31, JP179.1
TXO8: AVR8.31, JP204.1
TXO9: AVR9.31, JP229.1
TXO10: AVR10.31, JP254.1
TXO11: AVR11.31, JP279.1
TXO12: AVR12.31, JP304.1
TXO13: AVR13.31, JP329.1
TXO14: AVR14.31, JP354.1
TXO15: AVR15.31, JP379.1
VBAT: C5.1, JP24.1, LDO.3, U2.3
VBAT1: C13.1, JP43.1, LDO1.3, U1.3
VBAT2: C20.1, JP68.1, LDO2.3, U3.3
VBAT3: C27.1, JP93.1, LDO3.3, U4.3
VBAT4: C34.1, JP118.1, LDO4.3, U5.3
VBAT5: C41.1, JP143.1, LDO5.3, U6.3
VBAT6: C48.1, JP168.1, LDO6.3, U7.3
VBAT7: C55.1, JP193.1, LDO7.3, U8.3
VBAT8: C62.1, JP218.1, LDO8.3, U9.3
VBAT9: C69.1, JP243.1, LDO9.3, U10.3
VBAT10: C76.1, JP268.1, LDO10.3, U11.3
VBAT11: C83.1, JP293.1, LDO11.3, U12.3
VBAT12: C90.1, JP318.1, LDO12.3, U13.3
VBAT13: C97.1, JP343.1, LDO13.3, U14.3
VBAT14: C104.1, JP368.1, LDO14.3, U15.3
VBAT15: C111.1, JP393.1, LDO15.3, U16.3
VIBR: JP23.1, Q2.3
VIBR1: JP44.1, Q4.3
VIBR2: JP69.1, Q6.3
VIBR3: JP94.1, Q8.3
VIBR4: JP119.1, Q10.3
VIBR5: JP144.1, Q12.3
VIBR6: JP169.1, Q14.3
VIBR7: JP194.1, Q16.3
VIBR8: JP219.1, Q18.3
VIBR9: JP244.1, Q20.3
VIBR10: JP269.1, Q22.3
VIBR11: JP294.1, Q24.3
VIBR12: JP319.1, Q26.3
VIBR13: JP344.1, Q28.3
VIBR14: JP369.1, Q30.3
VIBR15: JP394.1, Q32.3
