avoccado/avoccado-pcb-avr/avoccado-gin/icsp/avoccado-avr-gin-icsp.brd

## EAGLE design avoccado-gin/icsp/avoccado-avr-gin-icsp.brd (2015-03-28)

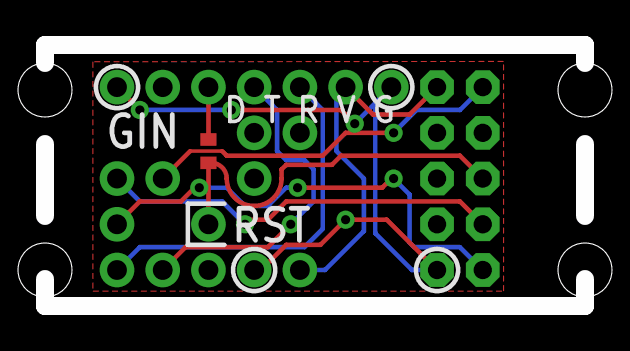
[picture p47: board avoccado-avr-gin-icsp.brd from above]

Board: 2 copper layers, 30.0 x 14.5 mm, 21 parts (1 on the bottom side), 9 nets.

Parts:
C1: C0402
TP1, TP3, TP4, TP5, TP8, TP13, TP17, TP18, TP19, TP20, TP21, TP22, TP23, TP24, TP25, TP26, TP28, TP29, TP30: PTR1PAD1-13; P1-13
U$1: AVR_SPI_PROG; AVR_ICSP

Connections:
3.3V: TP8.TP, TP22.TP, TP28.TP, U$1.2
DTR: C1.2, TP1.TP
GND: TP18.TP, TP24.TP, TP29.TP, U$1.10
MISO: TP21.TP, U$1.9
MOSI: TP19.TP, U$1.1
RESET: C1.1, TP23.TP, U$1.5
RXI: TP3.TP, TP25.TP
SCK: TP20.TP, U$1.7
TXO: TP5.TP, TP26.TP
