avoccado/avoccado-pcb-avr/avoccado-kane/avoccado-avr-pcb-kane-panel/avoccado-avr-pcb-kane-a1-panel.brd

## EAGLE design avoccado-kane/avoccado-avr-pcb-kane-panel/avoccado-avr-pcb-kane-a1-panel.brd (2014-12-11)

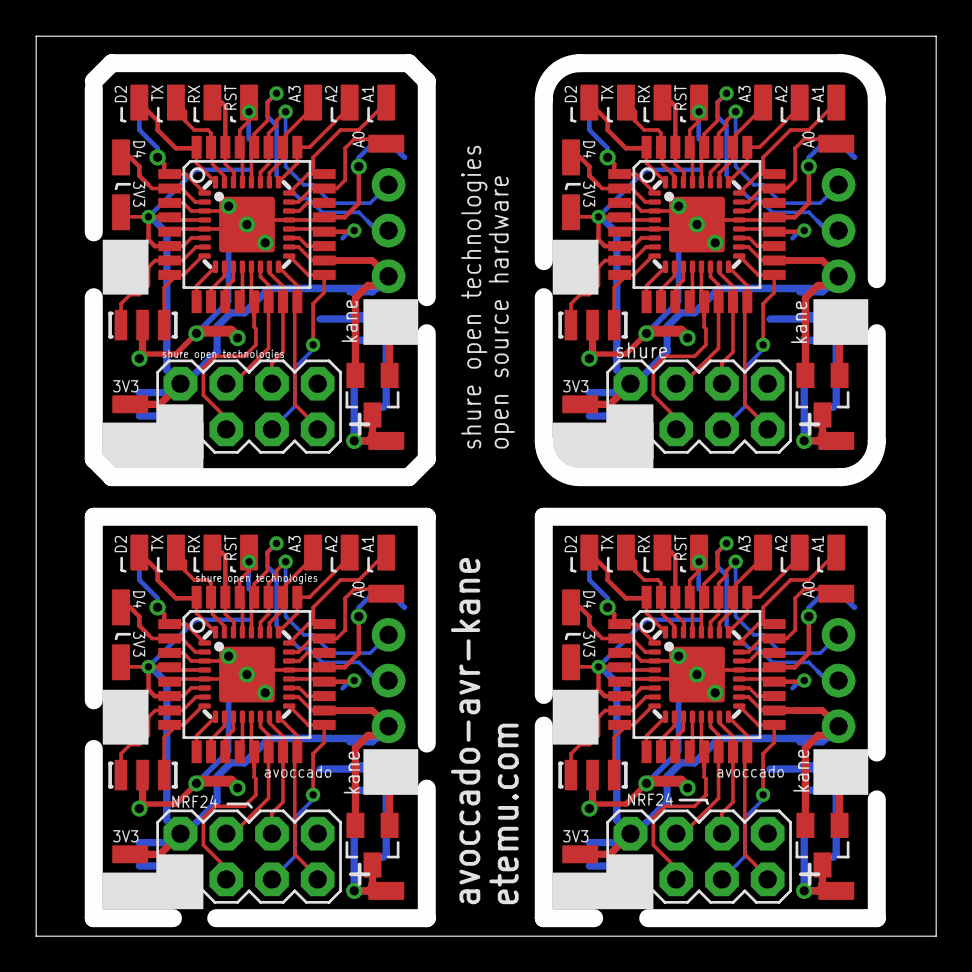
[picture p48: board avoccado-avr-pcb-kane-a1-panel.brd from above]

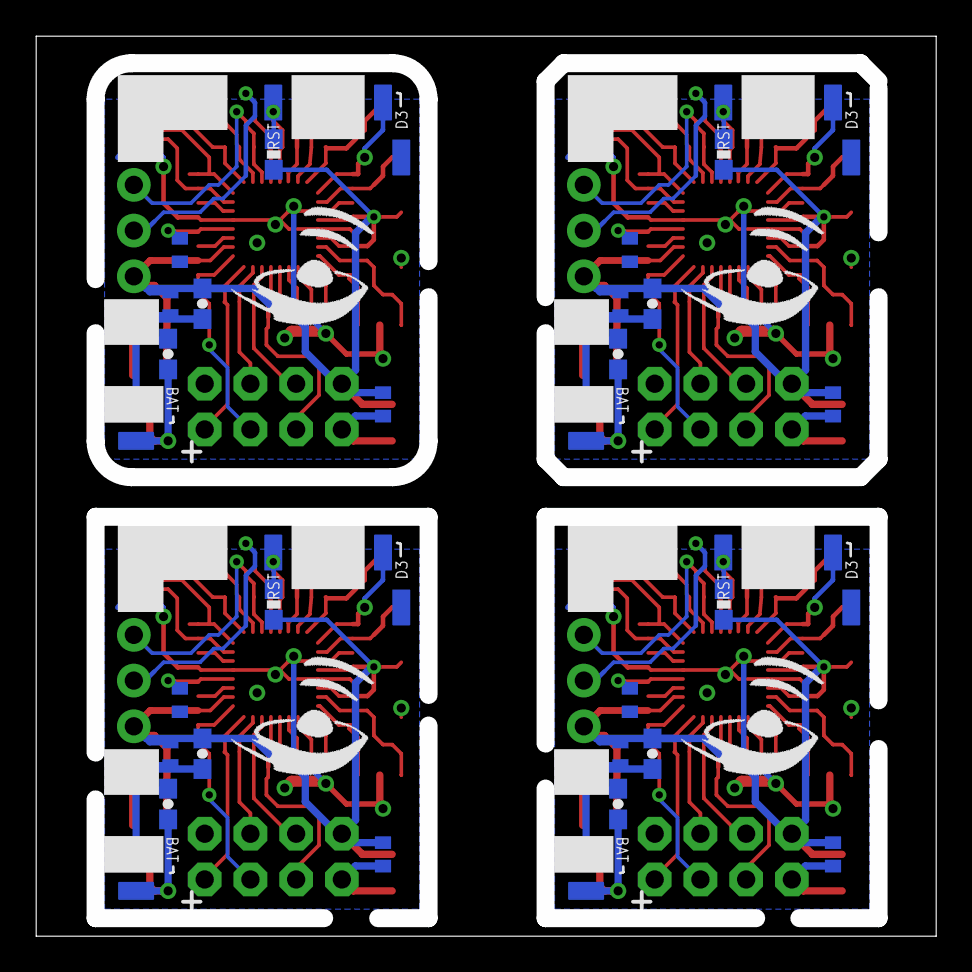
[picture p49: board avoccado-avr-pcb-kane-a1-panel.brd from below]

Board: 2 copper layers, 50.0 x 50.0 mm, 148 parts (68 on the bottom side), 116 nets.

Parts:
AVR, AVR1, AVR2, AVR3: ATMEGA328P; TQFP32-08
C1, C3, C4, C6, C7, C10, C11, C12, C13, C16, C17, C18: 0.1uF; C0402
C2, C5, C8, C9, C14, C15, C19, C20: 4.7uF; 0603-CAP
IC1, IC2, IC3, IC5: ATMEGA328P-20MU; MLF32
JP1, JP2, JP3, JP4, JP5, JP6, JP7, JP8, JP9, JP10, JP11, JP12, JP13, JP14, JP15, JP16, JP17, JP18, JP19, JP20, JP21, JP22, JP23, JP24, JP25, JP26, JP27, JP28, JP29, JP30, JP31, JP32, JP33, JP34, JP35, JP36, JP37, JP38, JP39, JP40, JP41, JP42, JP43, JP44, JP45, JP46, JP47, JP48, JP49, JP50, JP51, JP52, JP53, JP54, JP55, JP56, JP57, JP58, JP59, JP60, JP61, JP62, JP63, JP64, JP65, JP66, JP67, JP68, JP69, JP70, JP71, JP72, JP73, JP74, JP75, JP76, JP77, JP78, JP79, JP80, JP81, JP82, JP83, JP84, JP85, JP86, JP87, JP88, JP89, JP90, JP91, JP92, JP93, JP94, JP95, JP96, JP97, JP98, JP99, JP100: M01SMD; LUXEON-PAD
LDO1, LDO2, LDO3, LDO4: MCP1703CB; SOT23
MPU1, MPU2, MPU3, MPU6050: 1X04_NO_SILK
NRF1, NRF2, NRF3, NRF24: M04X2; 2X4
Q1, Q2, Q3, Q4: 16MHz; RESONATOR-SMD
R1, R2, R3, R4: 10K; 0603-RES

Connections:
3V1: AVR1.4, AVR1.6, AVR1.18, C4.1, C6.2, C9.1, IC1.4, IC1.6, IC1.18, JP26.P$1, JP32.P$1, LDO2.2, MPU1.2, NRF1.2, R1.2
3V2: AVR2.4, AVR2.6, AVR2.18, C11.1, C12.2, C15.1, IC2.4, IC2.6, IC2.18, JP51.P$1, JP57.P$1, LDO3.2, MPU2.2, NRF2.2, R3.2
3V3: AVR.4, AVR.6, AVR.18, C3.2, C5.1, C10.1, IC5.4, IC5.6, IC5.18, JP1.P$1, JP8.P$1, LDO1.2, MPU6050.2, NRF24.2, R2.2
3V4: AVR3.4, AVR3.6, AVR3.18, C16.1, C17.2, C20.1, IC3.4, IC3.6, IC3.18, JP76.P$1, JP82.P$1, LDO4.2, MPU3.2, NRF3.2, R4.2
A0: AVR.23, IC5.23, JP9.P$1
A1: AVR.24, IC5.24, JP10.P$1
A2: AVR.25, IC5.25, JP11.P$1
A3: AVR.26, IC5.26, JP3.P$1
A4: AVR.27, IC5.27, MPU6050.4
A5: AVR.28, IC5.28, MPU6050.3
A6: AVR.19, IC5.19
A7: AVR.22, IC5.22
A8: AVR1.28, IC1.28, MPU1.3
A9: AVR1.27, IC1.27, MPU1.4
A10: AVR1.26, IC1.26, JP35.P$1
A11: AVR1.25, IC1.25, JP36.P$1
A12: AVR1.24, IC1.24, JP34.P$1
A13: AVR1.23, IC1.23, JP33.P$1
A14: AVR1.19, IC1.19
A15: AVR1.22, IC1.22
A16: AVR2.28, IC2.28, MPU2.3
A17: AVR2.27, IC2.27, MPU2.4
A18: AVR2.26, IC2.26, JP60.P$1
A19: AVR2.25, IC2.25, JP61.P$1
A20: AVR2.24, IC2.24, JP59.P$1
A21: AVR2.23, IC2.23, JP58.P$1
A22: AVR2.19, IC2.19
A23: AVR2.22, IC2.22
A24: AVR3.28, IC3.28, MPU3.3
A25: AVR3.27, IC3.27, MPU3.4
A26: AVR3.26, IC3.26, JP85.P$1
A27: AVR3.25, IC3.25, JP86.P$1
A28: AVR3.24, IC3.24, JP84.P$1
A29: AVR3.23, IC3.23, JP83.P$1
A30: AVR3.19, IC3.19
A31: AVR3.22, IC3.22
AREF: AVR.20, C1.2, IC5.20
AREF1: AVR1.20, C7.2, IC1.20
AREF2: AVR2.20, C13.2, IC2.20
AREF3: AVR3.20, C18.2, IC3.20
D1: AVR1.13, IC1.13, NRF1.3
D2: AVR.32, IC5.32, JP15.P$1
D3: AVR.1, IC5.1, JP13.P$1
D4: AVR.2, IC5.2, JP14.P$1
D5: AVR.9, IC5.9
D6: AVR.10, IC5.10
D7: AVR.11, IC5.11
D8: AVR.12, IC5.12
D9: AVR.13, IC5.13, NRF24.3
D10: AVR.14, IC5.14, NRF24.4
D11: AVR1.12, IC1.12
D12: AVR1.32, IC1.32, JP40.P$1
D13: AVR1.1, IC1.1, JP38.P$1
D14: AVR1.2, IC1.2, JP39.P$1
D15: AVR1.9, IC1.9
D16: AVR1.10, IC1.10
D17: AVR1.11, IC1.11
D18: AVR1.14, IC1.14, NRF1.4
D19: AVR2.13, IC2.13, NRF2.3
D20: AVR2.12, IC2.12
D21: AVR2.32, IC2.32, JP65.P$1
D22: AVR2.1, IC2.1, JP63.P$1
D23: AVR2.2, IC2.2, JP64.P$1
D24: AVR2.9, IC2.9
D25: AVR2.10, IC2.10
D26: AVR2.11, IC2.11
D27: AVR2.14, IC2.14, NRF2.4
D28: AVR3.13, IC3.13, NRF3.3
D29: AVR3.12, IC3.12
D30: AVR3.32, IC3.32, JP90.P$1
D31: AVR3.1, IC3.1, JP88.P$1
D32: AVR3.2, IC3.2, JP89.P$1
D33: AVR3.9, IC3.9
D34: AVR3.10, IC3.10
D35: AVR3.11, IC3.11
D36: AVR3.14, IC3.14, NRF3.4
GND: AVR.3, AVR.5, AVR.21, C1.1, C2.2, C3.1, C5.2, C10.2, IC5.3, IC5.5, IC5.21, JP7.P$1, JP12.P$1, JP16.P$1, JP17.P$1, JP18.P$1, JP19.P$1, JP20.P$1, JP21.P$1, JP22.P$1, JP23.P$1, LDO1.1, MPU6050.1, NRF24.1, Q1.2
GND1: AVR1.3, AVR1.5, AVR1.21, C4.2, C6.1, C7.1, C8.2, C9.2, IC1.3, IC1.5, IC1.21, JP31.P$1, JP37.P$1, JP41.P$1, JP42.P$1, JP43.P$1, JP44.P$1, JP45.P$1, JP46.P$1, JP47.P$1, JP48.P$1, LDO2.1, MPU1.1, NRF1.1, Q2.2
GND2: AVR2.3, AVR2.5, AVR2.21, C11.2, C12.1, C13.1, C14.2, C15.2, IC2.3, IC2.5, IC2.21, JP56.P$1, JP62.P$1, JP66.P$1, JP67.P$1, JP68.P$1, JP69.P$1, JP70.P$1, JP71.P$1, JP72.P$1, JP73.P$1, LDO3.1, MPU2.1, NRF2.1, Q3.2
GND3: AVR3.3, AVR3.5, AVR3.21, C16.2, C17.1, C18.1, C19.2, C20.2, IC3.3, IC3.5, IC3.21, JP81.P$1, JP87.P$1, JP91.P$1, JP92.P$1, JP93.P$1, JP94.P$1, JP95.P$1, JP96.P$1, JP97.P$1, JP98.P$1, LDO4.1, MPU3.1, NRF3.1, Q4.2
MISO: AVR.16, IC5.16, NRF24.7
MISO1: AVR1.16, IC1.16, NRF1.7
MISO2: AVR2.16, IC2.16, NRF2.7
MISO3: AVR3.16, IC3.16, NRF3.7
MOSI: AVR.15, IC5.15, NRF24.6
MOSI1: AVR1.15, IC1.15, NRF1.6
MOSI2: AVR2.15, IC2.15, NRF2.6
MOSI3: AVR3.15, IC3.15, NRF3.6
unnamed: AVR.8, IC5.8, Q1.1
unnamed: AVR.7, IC5.7, Q1.3
unnamed: AVR1.8, IC1.8, Q2.1
unnamed: AVR1.7, IC1.7, Q2.3
unnamed: AVR2.8, IC2.8, Q3.1
unnamed: AVR2.7, IC2.7, Q3.3
unnamed: AVR3.8, IC3.8, Q4.1
unnamed: AVR3.7, IC3.7, Q4.3
RESET: AVR.29, IC5.29, JP5.P$1, JP25.P$1, R2.1
RESET1: AVR1.29, IC1.29, JP29.P$1, JP50.P$1, R1.1
RESET2: AVR2.29, IC2.29, JP54.P$1, JP75.P$1, R3.1
RESET3: AVR3.29, IC3.29, JP79.P$1, JP100.P$1, R4.1
RXI: AVR.30, IC5.30, JP2.P$1
RXI1: AVR1.30, IC1.30, JP27.P$1
RXI2: AVR2.30, IC2.30, JP52.P$1
RXI3: AVR3.30, IC3.30, JP77.P$1
SCK: AVR.17, IC5.17, NRF24.5
SCK1: AVR1.17, IC1.17, NRF1.5
SCK2: AVR2.17, IC2.17, NRF2.5
SCK3: AVR3.17, IC3.17, NRF3.5
TXO: AVR.31, IC5.31, JP4.P$1
TXO1: AVR1.31, IC1.31, JP28.P$1
TXO2: AVR2.31, IC2.31, JP53.P$1
TXO3: AVR3.31, IC3.31, JP78.P$1
VBAT: C2.1, JP6.P$1, JP24.P$1, LDO1.3
VBAT1: C8.1, JP30.P$1, JP49.P$1, LDO2.3
VBAT2: C14.1, JP55.P$1, JP74.P$1, LDO3.3
VBAT3: C19.1, JP80.P$1, JP99.P$1, LDO4.3
